MakersAsylumIndia/FireFly/datasheets/rgb_firefly_sch1.png

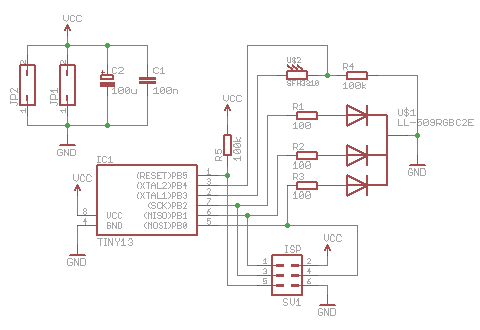
datasheets/rgb_firefly_sch1.png
