MakersAsylumIndia/FireFly/kicad_v1/firefly/images/firefly_01.png

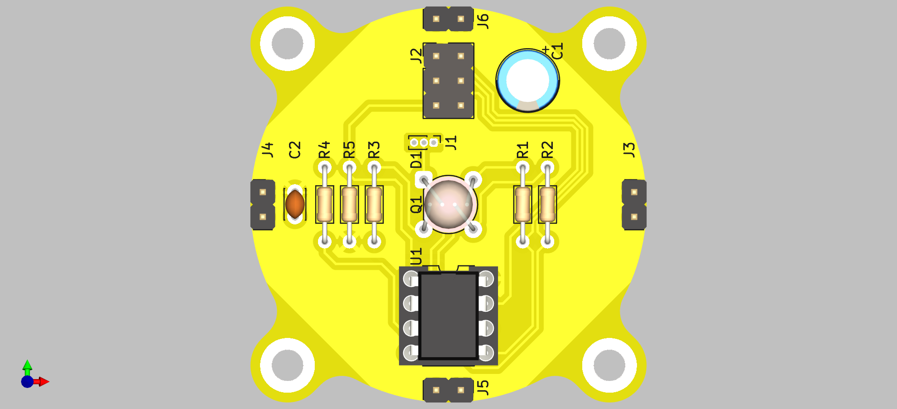
kicad_v1/firefly/images/firefly_01.png
