MakersAsylumIndia/FireFly/kicad_v1/firefly/images/firefly_02.png

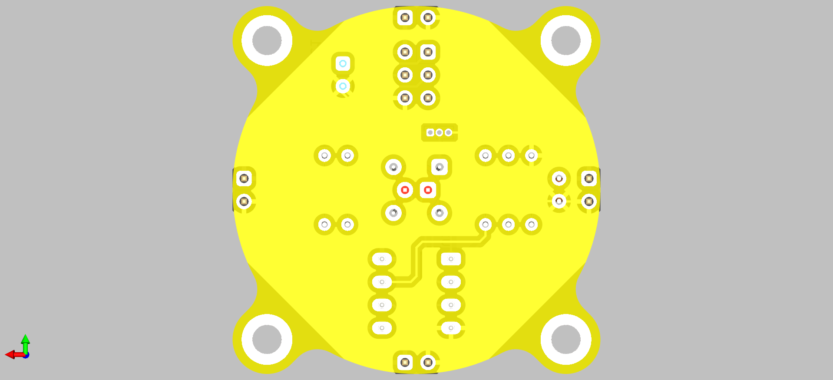
kicad_v1/firefly/images/firefly_02.png
