MakersAsylumIndia/FireFly/kicad_v1/firefly/images/firefly_03.png

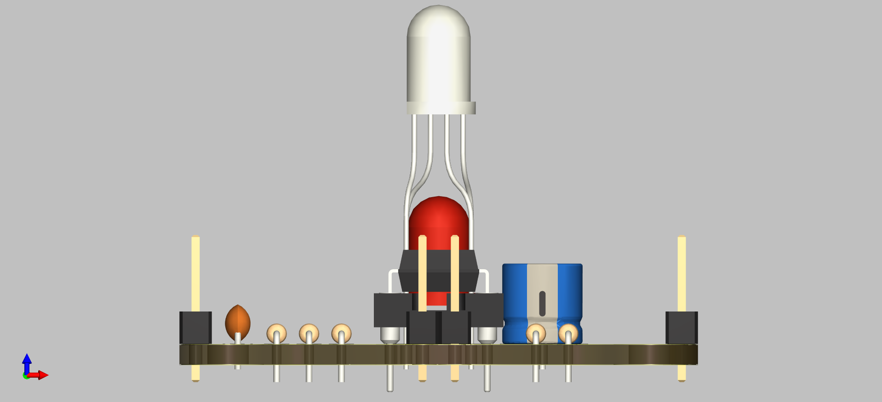
kicad_v1/firefly/images/firefly_03.png
