MakersAsylumIndia/FireFly/kicad_v1/firefly/images/firefly_04.png

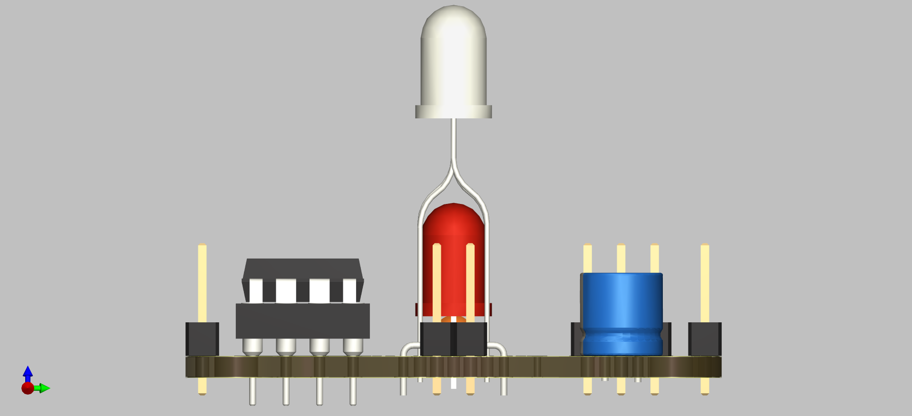
kicad_v1/firefly/images/firefly_04.png
