MakersAsylumIndia/FireFly/kicad_v1/firefly/3d_models/C_Disc_D3.0mm_W2.0mm_P2.50mm.step

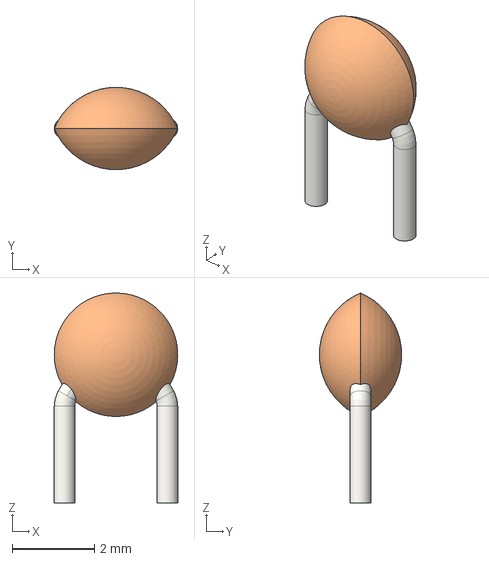
[picture p39: CAD file, 2023-04-18]
kicad_v1/firefly/3d_models/C_Disc_D3.0mm_W2.0mm_P2.50mm.step
3.00 x 2.00 x 5.10 mm
