MakersAsylumIndia/FireFly/kicad_v1/firefly/3d_models/PinHeader_1x02_P2.54mm_Vertical.step

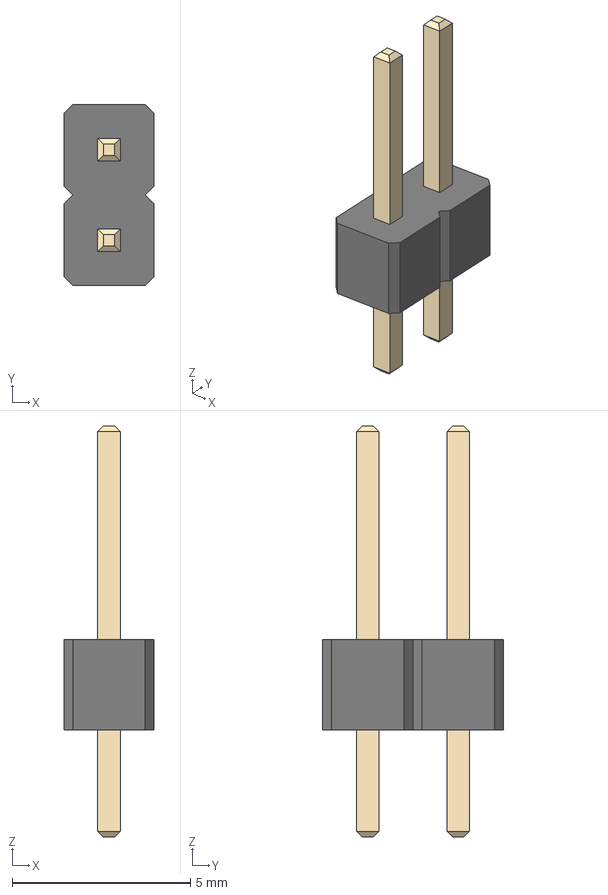
[picture p40: CAD file, 2023-04-18]
kicad_v1/firefly/3d_models/PinHeader_1x02_P2.54mm_Vertical.step
2.54 x 5.08 x 11.5 mm
