MakersAsylumIndia/FireFly/fabricate/renders/firefly_v1_01.png

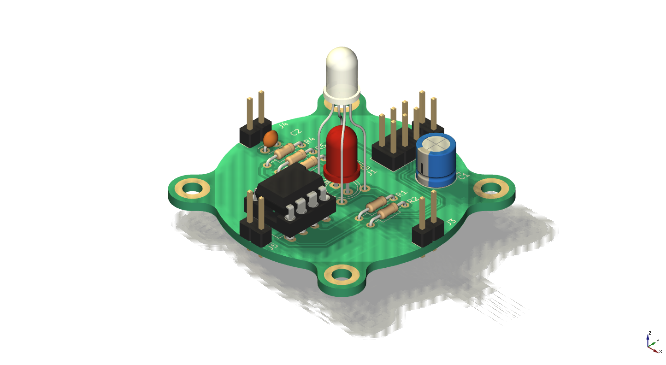
fabricate/renders/firefly_v1_01.png
