MakersAsylumIndia/FireFly/fabricate/renders/firefly_v1_02.png

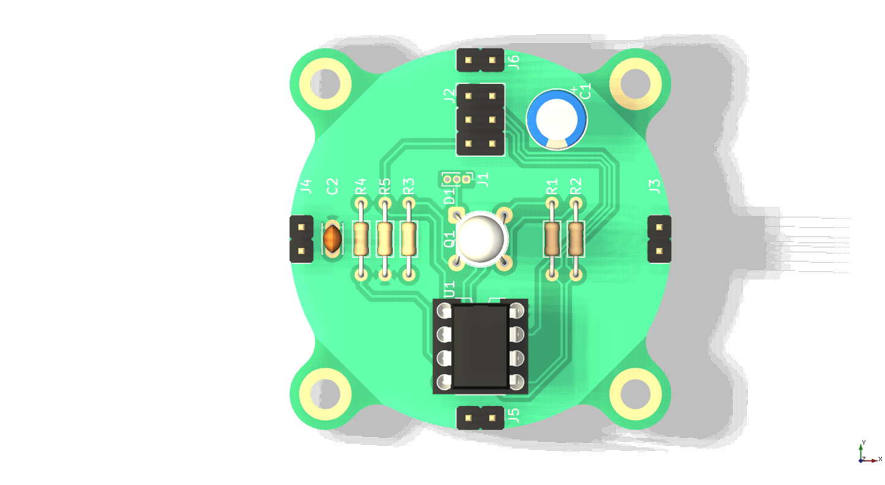
fabricate/renders/firefly_v1_02.png
