MakersAsylumIndia/FireFly/fabricate/renders/firefly_v1_07.png

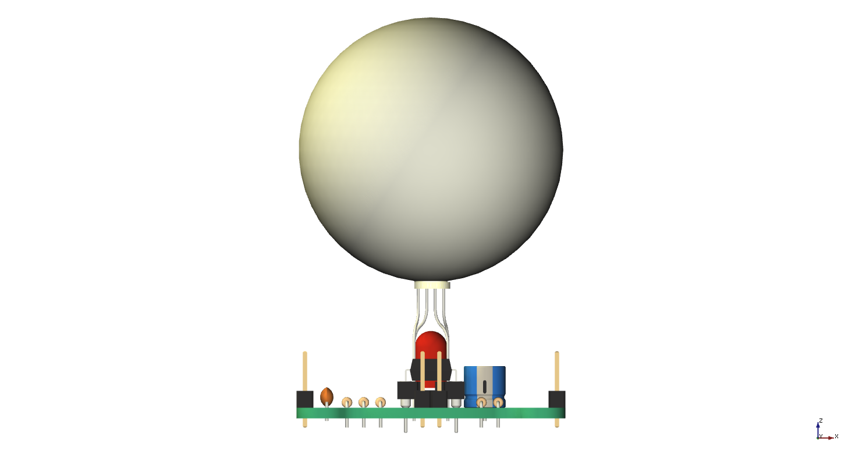
fabricate/renders/firefly_v1_07.png
