MakersAsylumIndia/FireFly/fabricate/renders/firefly_v1_grid_01.png

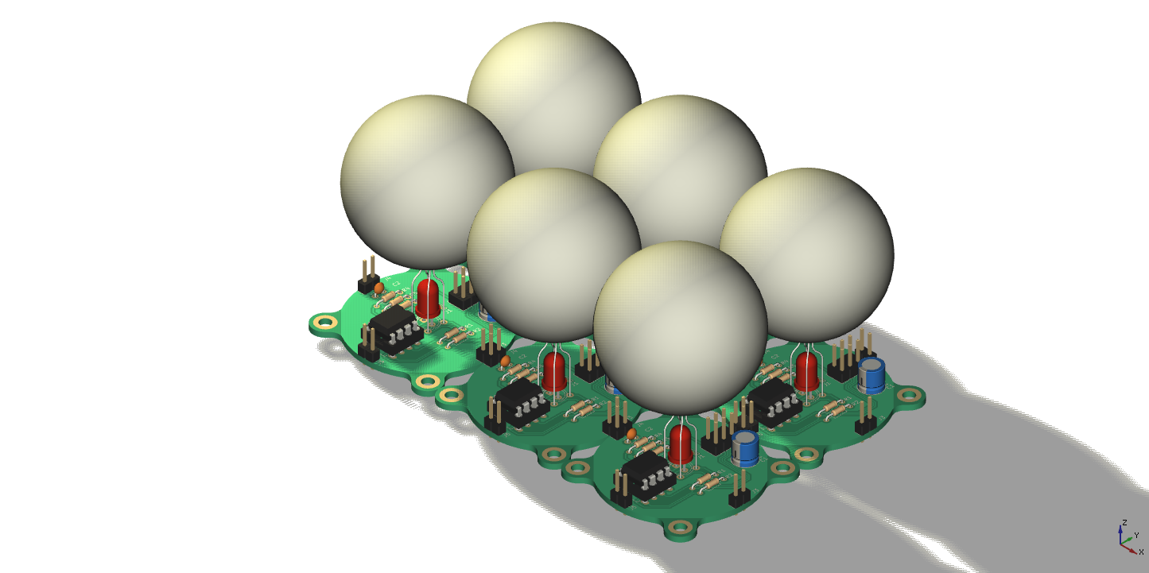
fabricate/renders/firefly_v1_grid_01.png
