MakersAsylumIndia/FireFly/fabricate/renders/firefly_v1_grid_03.png

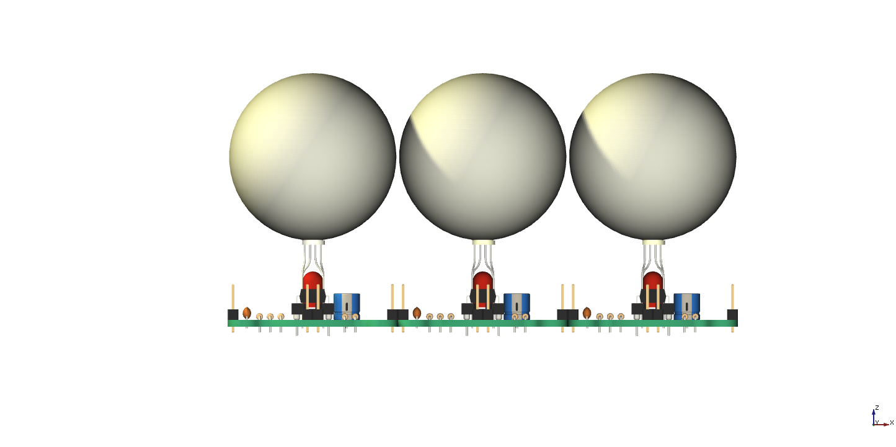
fabricate/renders/firefly_v1_grid_03.png
