MakersAsylumIndia/FireFly/fabricate/renders/firefly_v1_grid_04.png

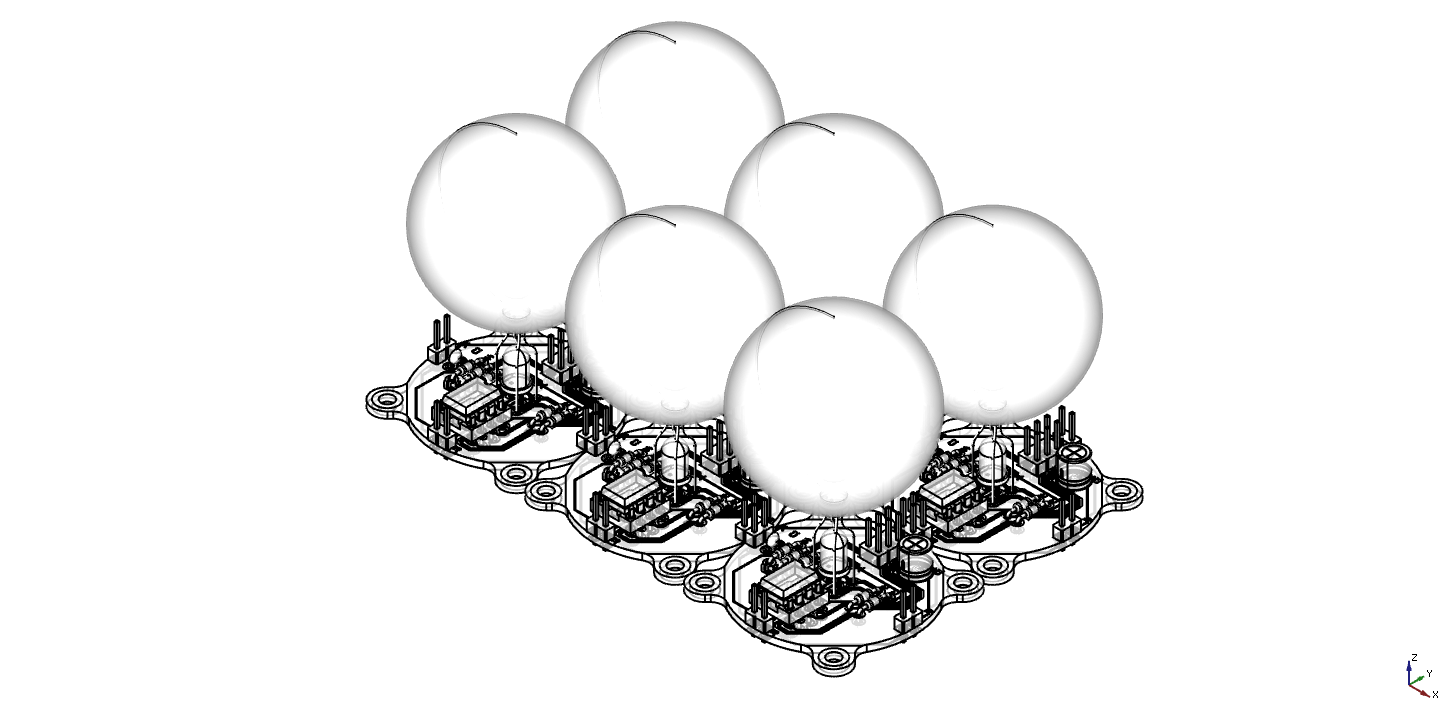
fabricate/renders/firefly_v1_grid_04.png
